banjomasterpete/alpha.ctrl/pcb files/AlphaCtrl.kicad_sch

## KiCad design pcb files/AlphaCtrl.kicad_sch (2024-07-19)

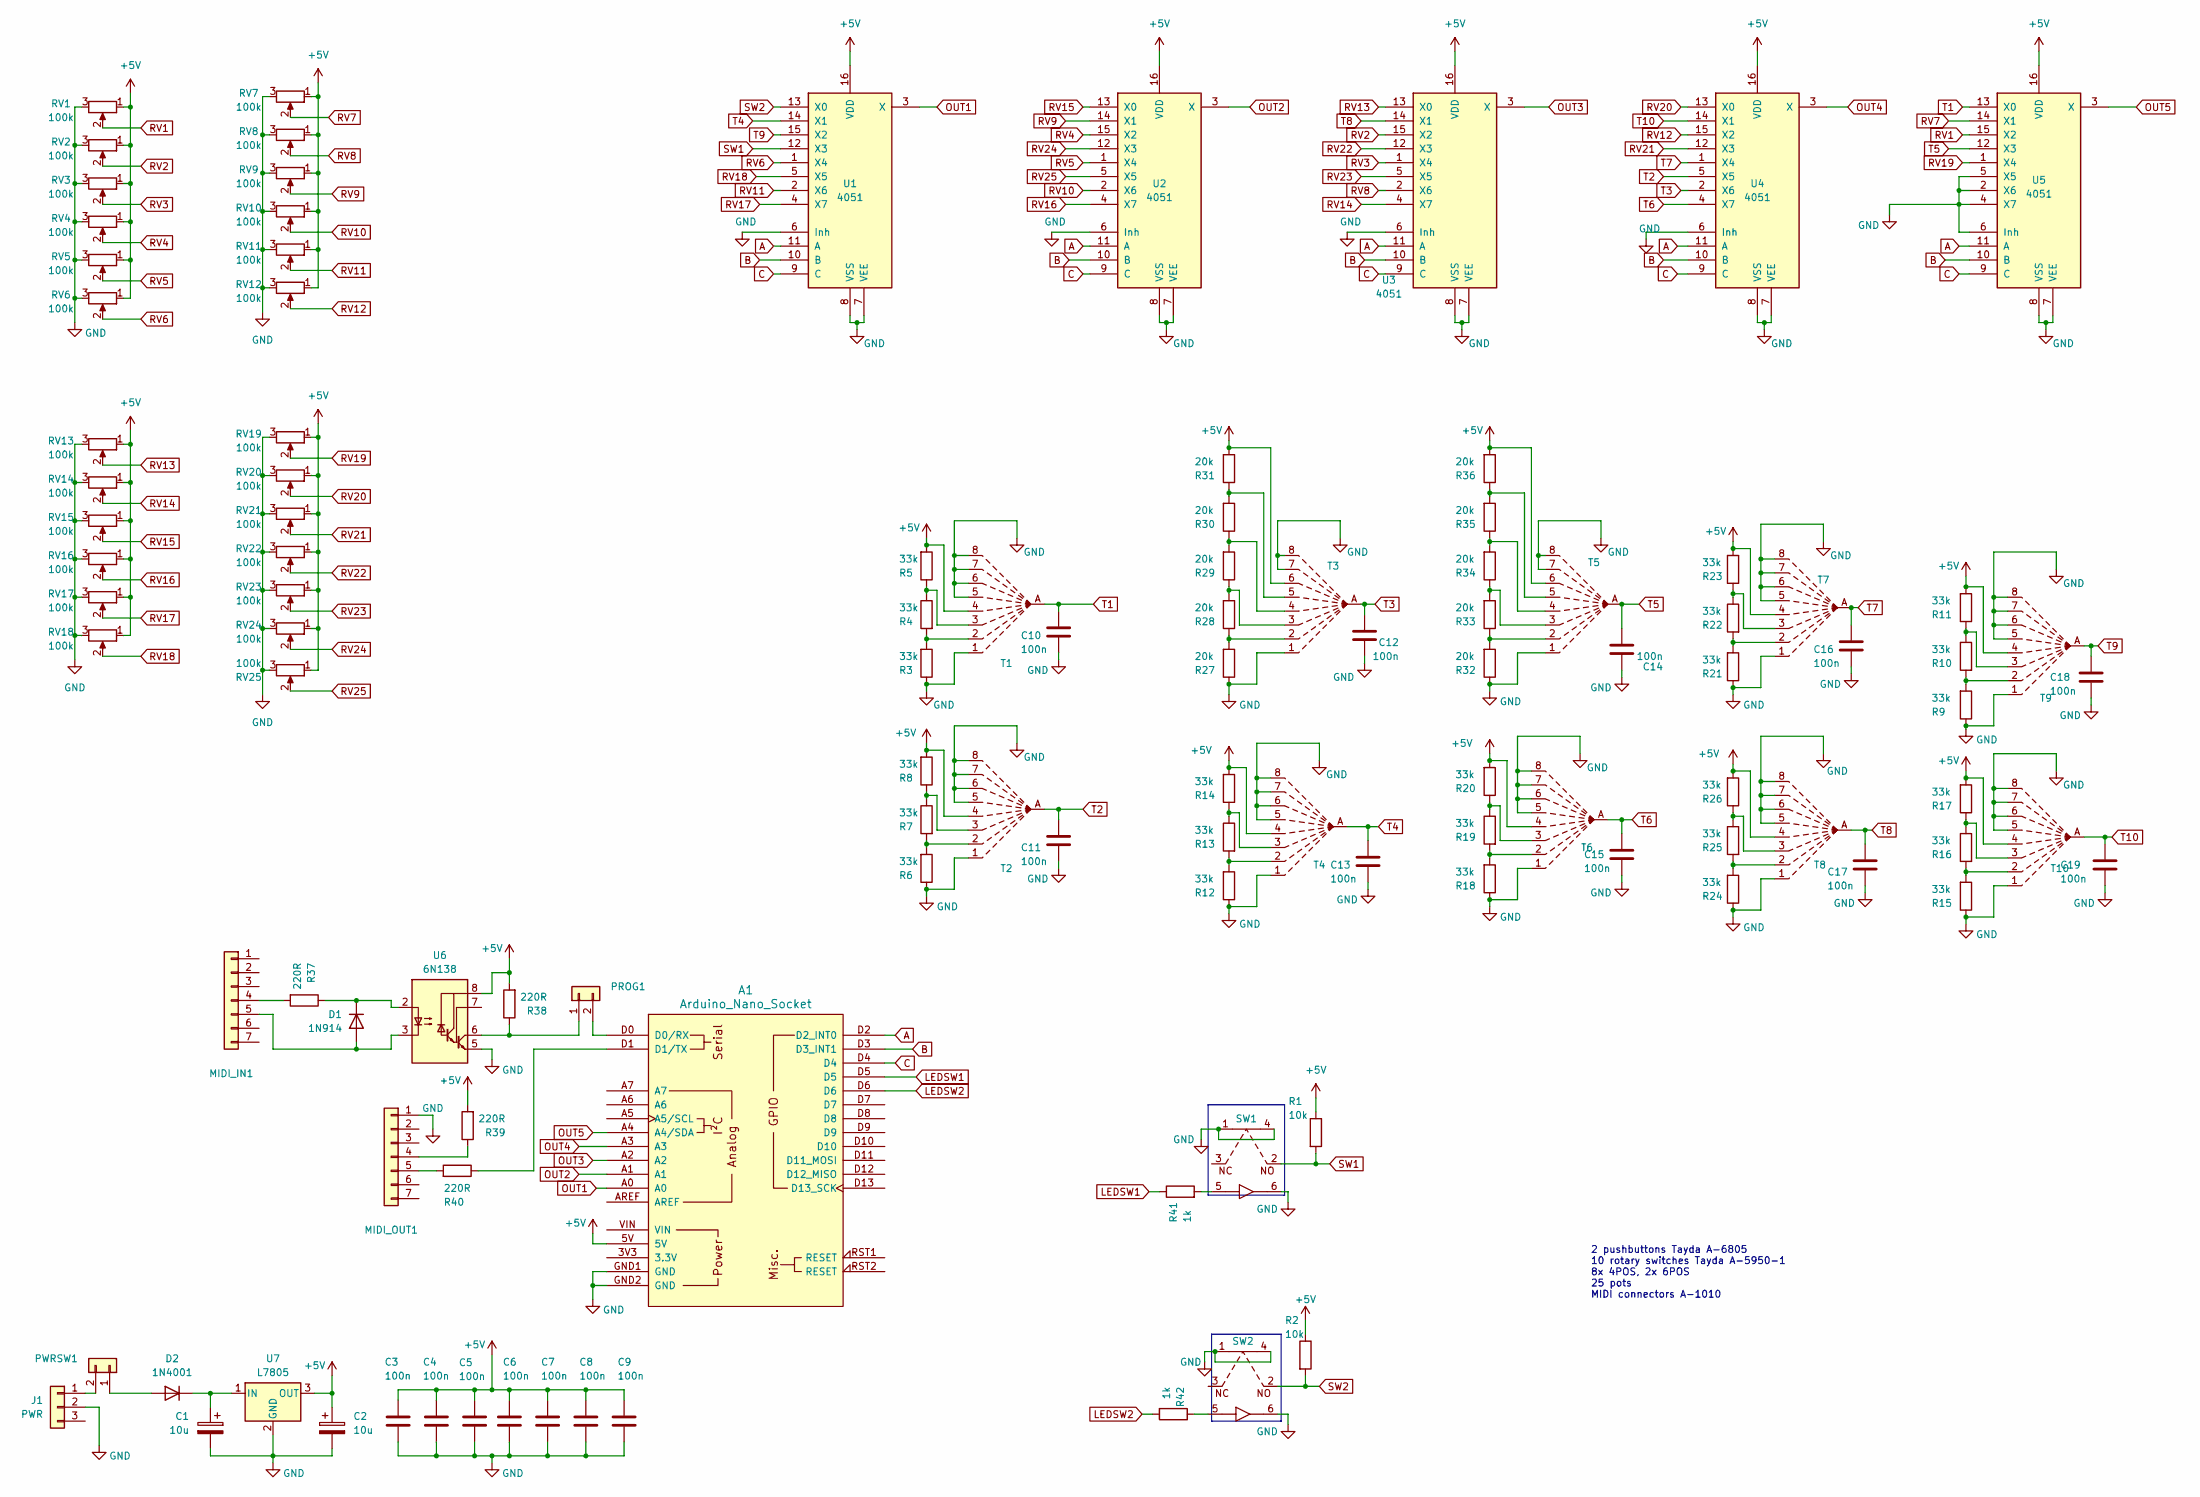
[picture p10: schematic AlphaCtrl.kicad_sch]

Parts:
A1: Arduino_Nano_Socket
C1, C2: 10u; CP_Radial_D6.3mm_P2.50mm
C3, C4, C5, C6, C7, C8, C9, C10, C11, C12, C13, C14, C15, C16, C17, C18, C19: 100n; C_Disc_D5.0mm_W2.5mm_P5.00mm
D1: 1N914; D_DO-35_SOD27_P7.62mm_Horizontal
D2: 1N4001; D_DO-41_SOD81_P10.16mm_Horizontal
J1: PWR; BarrelJack_Horizontal
MIDI_IN1: MIDI
MIDI_OUT1: MIDI
PROG1: PinHeader_1x02_P2.54mm_Vertical
PWRSW1: PinHeader_1x02_P2.54mm_Vertical
R1, R2: 10k; R_Axial_DIN0207_L6.3mm_D2.5mm_P10.16mm_Horizontal
R3, R4, R5, R6, R7, R8, R9, R10, R11, R12, R13, R14, R15, R16, R17, R18, R19, R20, R21, R22, R23, R24, R25, R26: 33k; R_Axial_DIN0207_L6.3mm_D2.5mm_P10.16mm_Horizontal
R27, R28, R29, R30, R31, R32, R33, R34, R35, R36: 20k; R_Axial_DIN0207_L6.3mm_D2.5mm_P10.16mm_Horizontal
R37, R38, R39, R40: 220R; R_Axial_DIN0207_L6.3mm_D2.5mm_P10.16mm_Horizontal
R41, R42: 1k; R_Axial_DIN0207_L6.3mm_D2.5mm_P10.16mm_Horizontal
RV1, RV2, RV3, RV4, RV5, RV6, RV7, RV8, RV9, RV10, RV11, RV12, RV13, RV14, RV15, RV16, RV17, RV18, RV19, RV20, RV21, RV22, RV23, RV24, RV25: 100k; Potentiometer_Bourns_PTV09A-1_Single_Vertical
SW1, SW2: JunoButtons
T1, T2, T3, T4, T5, T6, T7, T8, T9, T10: Switch_Rotary 8POS
U1, U2, U3, U4, U5: 4051; DIP-16_W7.62mm_Socket_LongPads
U6: 6N138; DIP-8_W7.62mm_LongPads
U7: L7805; TO-220-3_Vertical

Connections:
+5V: A1.5V, C2.1, C3.1, C4.1, C5.1, C6.1, C7.1, C8.1, C9.1, R1.1, R2.1, R5.2, R8.2, R11.2, R14.2, R17.2, R20.2, R23.2, R26.2, R31.2, R36.2, R38.2, R39.2, RV1.1, RV2.1, RV3.1, RV4.1, RV5.1, RV6.1, RV7.1, RV8.1, RV9.1, RV10.1, RV11.1, RV12.1, RV13.1, RV14.1, RV15.1, RV16.1, RV17.1, RV18.1, RV19.1, RV20.1, RV21.1, RV22.1, RV23.1, RV24.1, RV25.1, T1.4, T2.4, T3.6, T4.4, T5.6, T6.4, T7.4, T8.4, T9.4, T10.4, U1.16 (VDD), U2.16 (VDD), U3.16 (VDD), U4.16 (VDD), U5.16 (VDD), U6.8 (VCC), U7.3 (OUT)
A: A1.D2 (D2_INT0), U1.11 (A), U2.11 (A), U3.11 (A), U4.11 (A), U5.11 (A)
B: A1.D3 (D3_INT1), U1.10 (B), U2.10 (B), U3.10 (B), U4.10 (B), U5.10 (B)
C: A1.D4, U1.9 (C), U2.9 (C), U3.9 (C), U4.9 (C), U5.9 (C)
GND: A1.GND1 (GND), A1.GND2 (GND), C1.2, C2.2, C3.2, C4.2, C5.2, C6.2, C7.2, C8.2, C9.2, C10.2, C11.2, C12.2, C13.2, C14.2, C15.2, C16.2, C17.2, C18.2, C19.2, J1.2, MIDI_OUT1.1, R3.1, R6.1, R9.1, R12.1, R15.1, R18.1, R21.1, R24.1, R27.1, R32.1, RV1.3, RV2.3, RV3.3, RV4.3, RV5.3, RV6.3, RV7.3, RV8.3, RV9.3, RV10.3, RV11.3, RV12.3, RV13.3, RV14.3, RV15.3, RV16.3, RV17.3, RV18.3, RV19.3, RV20.3, RV21.3, RV22.3, RV23.3, RV24.3, RV25.3, SW1.1, SW1.4, SW1.6, SW2.1, SW2.4, SW2.6, T1.1, T1.5, T1.6, T1.7, T1.8, T2.1, T2.5, T2.6, T2.7, T2.8, T3.1, T3.7, T3.8, T4.1, T4.5, T4.6, T4.7, T4.8, T5.1, T5.7, T5.8, T6.1, T6.5, T6.6, T6.7, T6.8, T7.1, T7.5, T7.6, T7.7, T7.8, T8.1, T8.5, T8.6, T8.7, T8.8, T9.1, T9.5, T9.6, T9.7, T9.8, T10.1, T10.5, T10.6, T10.7, T10.8, U1.6 (Inh), U1.7 (VEE), U1.8 (VSS), U2.6 (Inh), U2.7 (VEE), U2.8 (VSS), U3.6 (Inh), U3.7 (VEE), U3.8 (VSS), U4.6 (Inh), U4.7 (VEE), U4.8 (VSS), U5.2 (X6), U5.4 (X7), U5.5 (X5), U5.6 (Inh), U5.7 (VEE), U5.8 (VSS), U6.5 (GND), U7.2 (GND)
LEDSW1: A1.D5, R41.1
LEDSW2: A1.D6, R42.2
unnamed: A1.D0 (D0/RX), PROG1.2
unnamed: A1.D1 (D1/TX), R40.1
unnamed: C1.1, D2.1 (K), U7.1 (IN)
unnamed: D1.1 (K), R37.1, U6.2 (C1)
unnamed: D1.2 (A), MIDI_IN1.5, U6.3 (C2)
unnamed: D2.2 (A), PWRSW1.1
unnamed: J1.1, PWRSW1.2
unnamed: MIDI_IN1.4, R37.2
unnamed: MIDI_OUT1.4, R39.1
unnamed: MIDI_OUT1.5, R40.2
unnamed: PROG1.1, R38.1, U6.6 (VO2)
unnamed: R3.2, R4.2, T1.2
unnamed: R4.1, R5.1, T1.3
unnamed: R6.2, R7.2, T2.2
unnamed: R7.1, R8.1, T2.3
unnamed: R10.1, R11.1, T9.3
unnamed: R9.2, R10.2, T9.2
unnamed: R12.2, R13.2, T4.2
unnamed: R13.1, R14.1, T4.3
unnamed: R15.2, R16.2, T10.2
unnamed: R16.1, R17.1, T10.3
unnamed: R18.2, R19.2, T6.2
unnamed: R19.1, R20.1, T6.3
unnamed: R21.2, R22.2, T7.2
unnamed: R22.1, R23.1, T7.3
unnamed: R24.2, R25.2, T8.2
unnamed: R25.1, R26.1, T8.3
unnamed: R27.2, R28.1, T3.2
unnamed: R28.2, R29.1, T3.3
unnamed: R29.2, R30.1, T3.4
unnamed: R30.2, R31.1, T3.5
unnamed: R32.2, R33.1, T5.2
unnamed: R33.2, R34.1, T5.3
unnamed: R34.2, R35.1, T5.4
unnamed: R35.2, R36.1, T5.5
unnamed: R41.2, SW1.5
unnamed: R42.1, SW2.5
OUT1: A1.A0, U1.3 (X)
OUT2: A1.A1, U2.3 (X)
OUT3: A1.A2, U3.3 (X)
OUT4: A1.A3, U4.3 (X)
OUT5: A1.A4 (A4/SDA), U5.3 (X)
RV1: RV1.2, U5.15 (X2)
RV2: RV2.2, U3.15 (X2)
RV3: RV3.2, U3.1 (X4)
RV4: RV4.2, U2.15 (X2)
RV5: RV5.2, U2.1 (X4)
RV6: RV6.2, U1.1 (X4)
RV7: RV7.2, U5.14 (X1)
RV8: RV8.2, U3.2 (X6)
RV9: RV9.2, U2.14 (X1)
RV10: RV10.2, U2.2 (X6)
RV11: RV11.2, U1.2 (X6)
RV12: RV12.2, U4.15 (X2)
RV13: RV13.2, U3.13 (X0)
RV14: RV14.2, U3.4 (X7)
RV15: RV15.2, U2.13 (X0)
RV16: RV16.2, U2.4 (X7)
RV17: RV17.2, U1.4 (X7)
RV18: RV18.2, U1.5 (X5)
RV19: RV19.2, U5.1 (X4)
RV20: RV20.2, U4.13 (X0)
RV21: RV21.2, U4.12 (X3)
RV22: RV22.2, U3.12 (X3)
RV23: RV23.2, U3.5 (X5)
RV24: RV24.2, U2.12 (X3)
RV25: RV25.2, U2.5 (X5)
SW1: R1.2, SW1.2, U1.12 (X3)
SW2: R2.2, SW2.2, U1.13 (X0)
T1: C10.1, T1.A, U5.13 (X0)
T2: C11.1, T2.A, U4.5 (X5)
T3: C12.1, T3.A, U4.2 (X6)
T4: C13.1, T4.A, U1.14 (X1)
T5: C14.1, T5.A, U5.12 (X3)
T6: C15.1, T6.A, U4.4 (X7)
T7: C16.1, T7.A, U4.1 (X4)
T8: C17.1, T8.A, U3.14 (X1)
T9: C18.1, T9.A, U1.15 (X2)
T10: C19.1, T10.A, U4.14 (X1)

Notes on the sheet:
2 pushbuttons Tayda A-6805 10 rotary switches Tayda A-5950-1 8x 4POS, 2x 6POS 25 pots MIDI connectors A-1010
